PaxInstruments/labwiz-board/electronics/versions/labwiz-board-0.2/labwiz-board.brd

## EAGLE design electronics/versions/labwiz-board-0.2/labwiz-board.brd (2016-09-06)

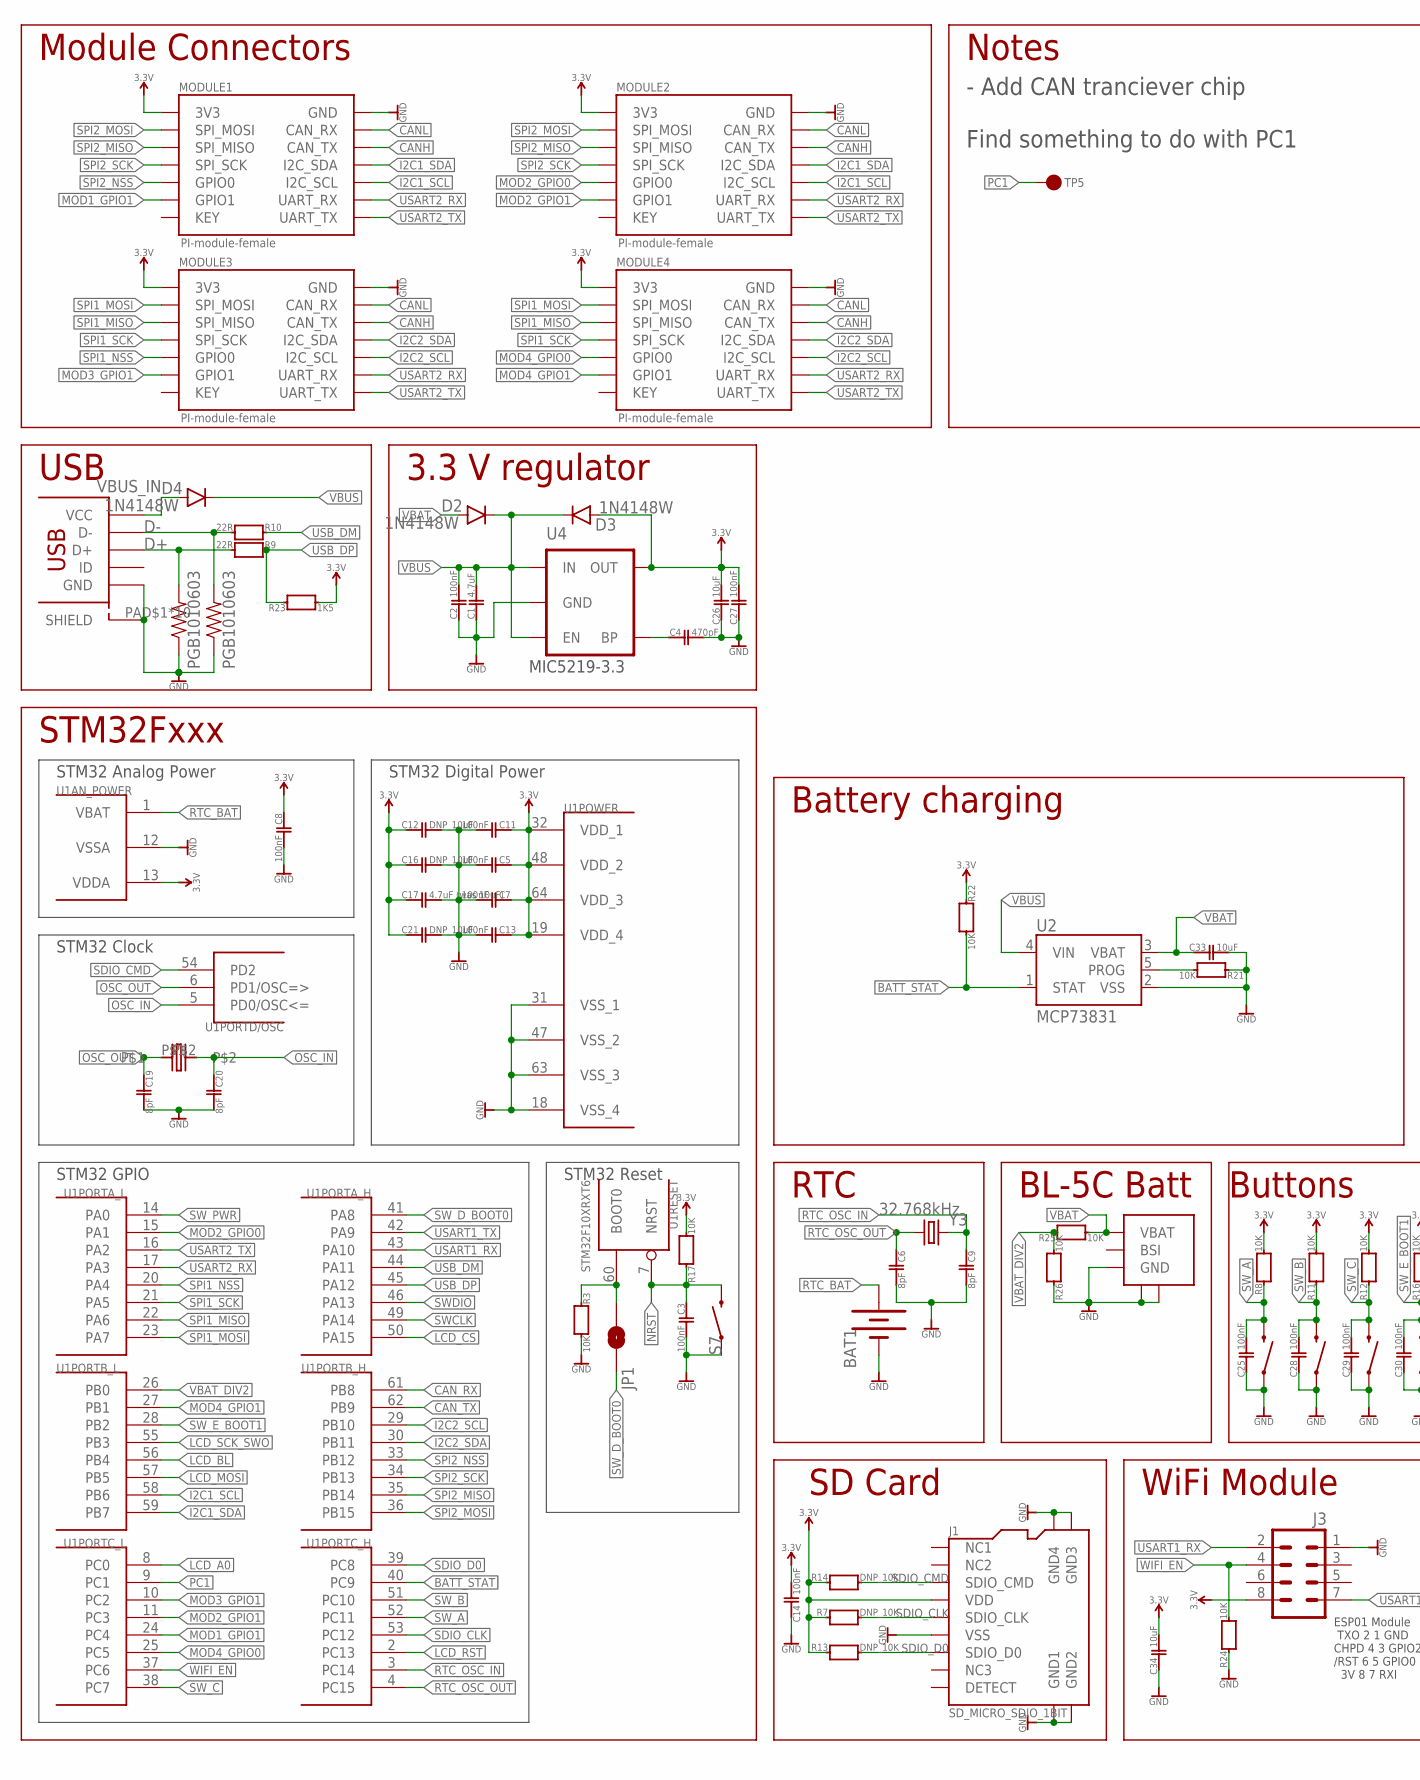
[picture p21: schematic labwiz-board.sch, sheet 1, part in row 1, column 1]

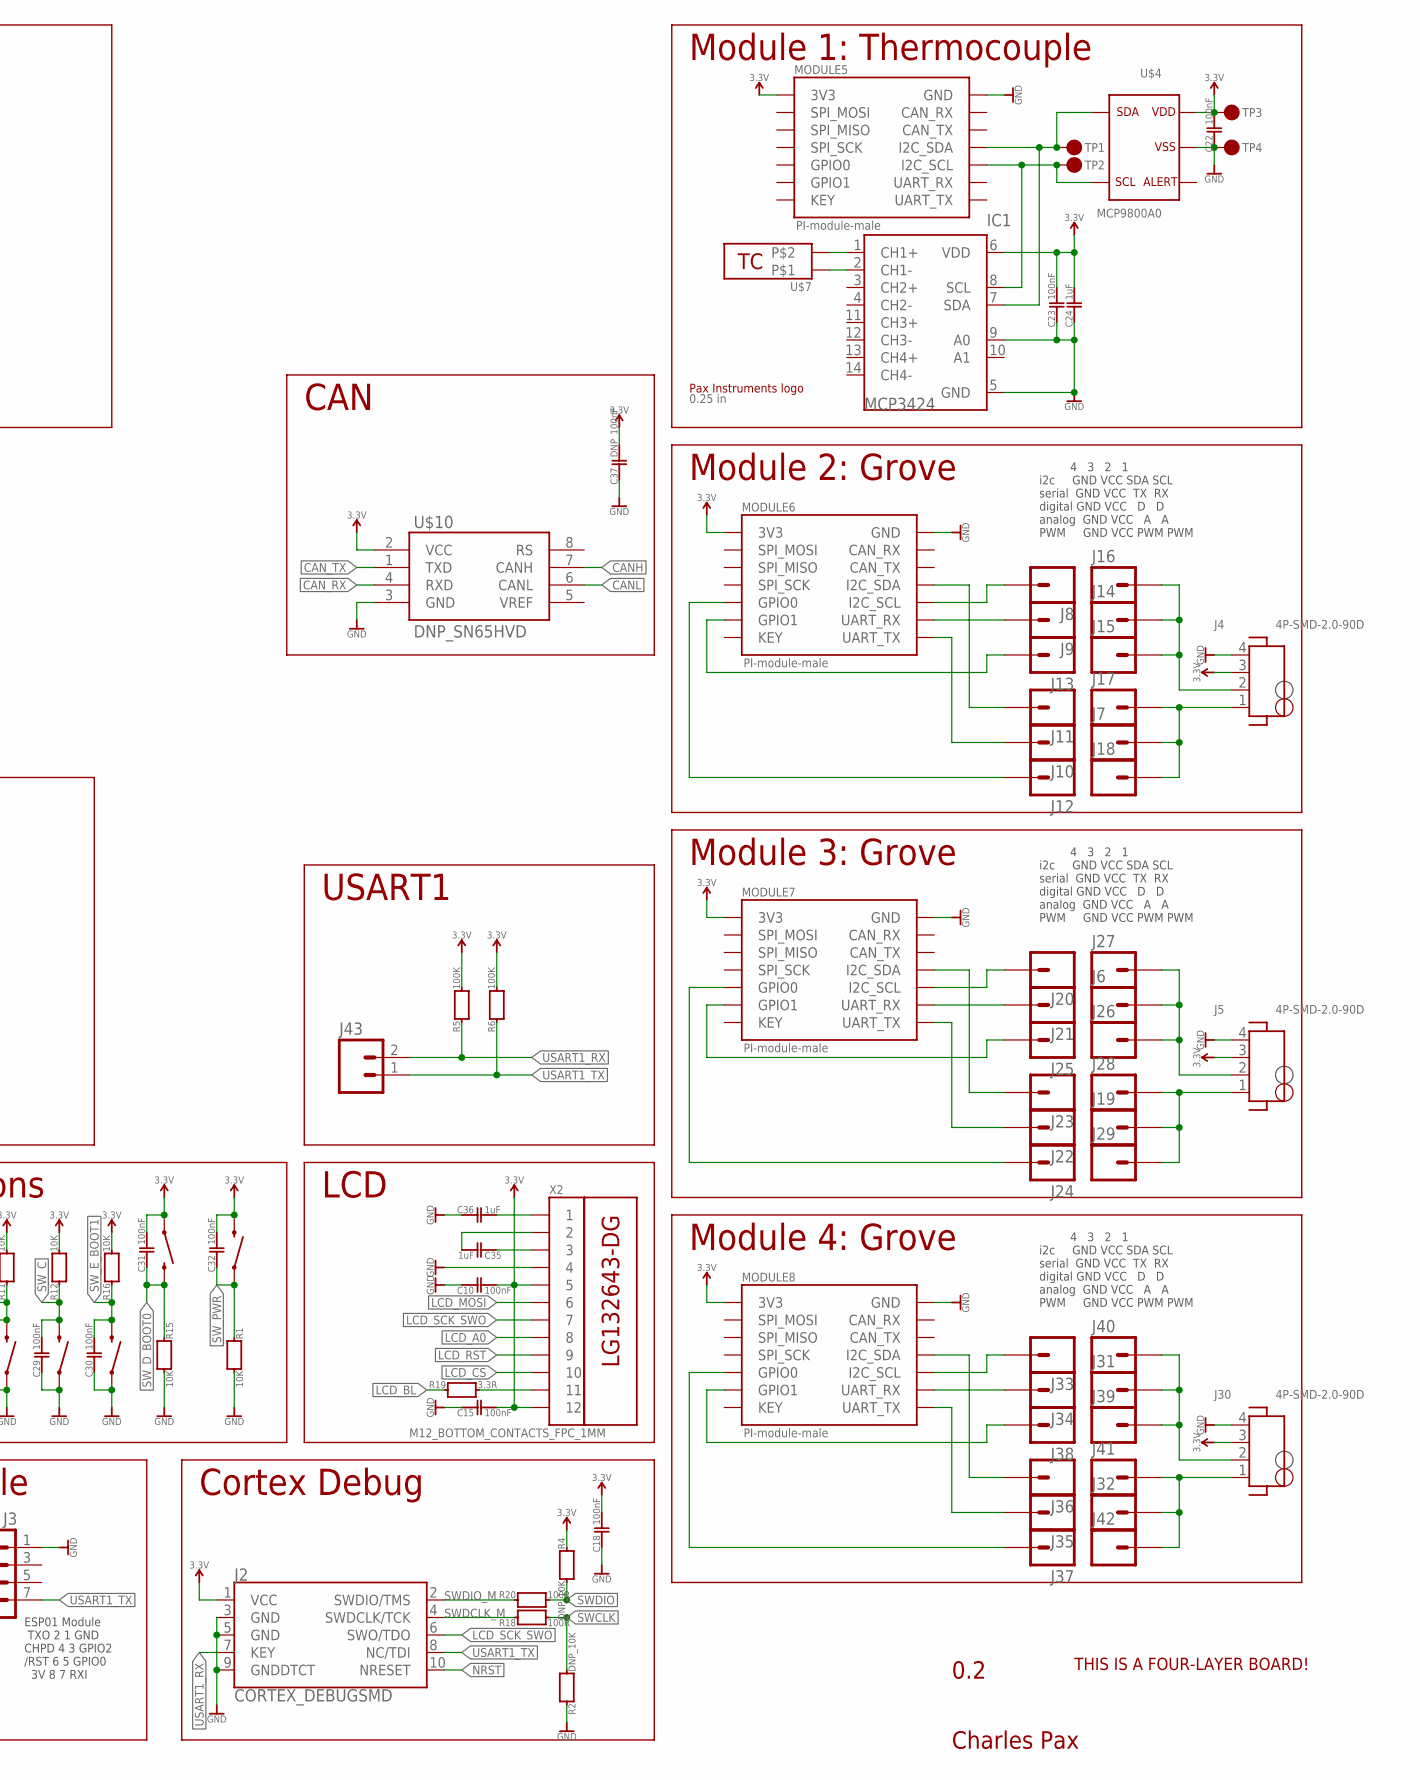
[picture p22: schematic labwiz-board.sch, sheet 1, part in row 1, column 2]

Parts:
BAT1: BATTERY12MM; BATTCON_12MM
C1: 4.7uF; 0402
C2, C3, C5, C7, C8, C10, C11, C13, C14, C15, C18, C22, C23, C25, C27, C28, C29, C30, C31, C32: 100nF; 0402
C4: 470pF; 0402
C6, C9, C19, C20: 8pF; 0402
C12, C16, C21: DNP_10uF; 0402
C17: 4.7uF (was 10uF); 0402
C24, C35, C36: 1uF; 0402
C26, C33, C34: 10uF; 0402
C37: DNP_100nF; 0402
D2, D3, D4: 1N4148W; SOD-123
IC1: MCP3424; SO14
J1: SD_MICRO_SDIO_1BIT; SD_MICRO_1
J2: CORTEX_DEBUGSMD; SAMTECH_FTSH-105-01
J3: M04X2; 2X4
J4, J5, J30: 4P-SMD-2.0-90D; HW4-SMD-2.0-90D
J6, J7, J8, J9, J10, J11, J12, J13, J14, J15, J16, J17, J18, J19, J20, J21, J22, J23, J24, J25, J26, J27, J28, J29, J31, J32, J33, J34, J35, J36, J37, J38, J39, J40, J41, J42: M01SMD-4.5X1.5; PAD-1.5X4.5
J43: M02PTH; 1X02
JP1: JUMPER-PAD-2-NOYES_SILK; PAD-JUMPER-2-NO_YES_SILK
MODULE1, MODULE2, MODULE3, MODULE4: PI-module-female; M07X2_2MM_EDGE
MODULE5, MODULE6, MODULE7, MODULE8: PI-module-male; M07X2_2MM_EDGE
R1, R3, R8, R11, R12, R15, R16, R17, R21, R22, R24, R25, R26: 10K; 0402
R2, R4, R7, R13, R14: DNP_10K; 0402
R5, R6: 100K; 0402
R9, R10: 22R; R0402
R18, R20: 100R; 0402
R19: 3.3R; 0402
R23: 1K5; R0402
S1, S2, S3, S4, S5, S6: SWITCH-MOMENTARY-2SMD; TACTILE_SWITCH_SMD; MPN RS-187R05A2-DS MT RT
S7: SWITCH-MOMENTARY-2SMD-3; TACTILE_SWITCH_SMD-3
TP1, TP2, TP3, TP4: M01_TH
TP5: M01_PAD_1MM; PAD_1MM
U1: STM32F10XRXT6; TQFP64
U2: MCP73831; SOT23-5
U4: MIC5219-3.3V; SOT23-5; MPN MIC5219-3.3YM5 TR
U$1: USB_MICROSMT+THRUHULE; USB_MICRO_THRUHOLE; MPN 10118194-0001LF
U$2: FOUR_LAYER_WARNING
U$3: BL-5C-CONNECTOR
U$4: MCP9800A0; SOT23-5L
U$5: LG132643-DG; MPN LG132643-DW
U$7: THERMOCOUPLE_MINI_INSIDE; THERMOCOUPLE_CLIP_INSIDE
U$9: NX3225GD
U$10: DNP_SN65HVD; SO08
U$13: 0.25 in; PAX-LOGO-0.25IN
X2: M12_BOTTOM_CONTACTS_FPC_1MM; FPC_12P_1MM
Y3: 32.768kHz; CRYSTAL-SMD-3.2X1.5MM
Z1, Z2: PGB1010603; SPARKFUN-RESISTORS_0603-RES; MPN PGB1010603NRHF

Connections:
3.3V: C5.1, C7.1, C8.1, C10.2, C11.1, C12.1, C13.1, C14.2, C15.2, C16.1, C17.1, C18.2, C21.1, C26.2, C27.2, C31.2, C32.2, C34.2, C37.2, D3.A, J1.4 (VDD), J2.1 (VCC), J3.8, MODULE1.P$1 (3V3), MODULE2.P$1 (3V3), MODULE3.P$1 (3V3), MODULE4.P$1 (3V3), R4.2, R5.1, R6.1, R7.2, R8.1, R11.1, R12.1, R13.2, R14.2, R16.1, R17.1, R22.2, R23.1, S4.1, S6.3 (2), U1.13 (VDDA), U1.19 (VDD_4), U1.32 (VDD_1), U1.48 (VDD_2), U1.64 (VDD_3), U4.5 (OUT), U$10.2 (VCC), X2.5, X2.12
3.3V_1: C22.2, C23.2, C24.2, IC1.6 (VDD), MODULE5.P$13 (3V3), TP3.P$1, U$4.1
3.3V_2: J4.3 (2), MODULE6.P$13 (3V3)
3.3V_3: J5.3 (2), MODULE7.P$13 (3V3)
3.3V_4: J30.3 (2), MODULE8.P$13 (3V3)
BATT_STAT: R22.1, U1.40 (PC9), U2.1 (STAT)
BOOT0: JP1.2, R3.2, U1.60 (BOOT0)
CANH: MODULE1.P$6 (CAN_TX), MODULE2.P$6 (CAN_TX), MODULE3.P$6 (CAN_TX), MODULE4.P$6 (CAN_TX), U$10.7 (CANH)
CANL: MODULE1.P$4 (CAN_RX), MODULE2.P$4 (CAN_RX), MODULE3.P$4 (CAN_RX), MODULE4.P$4 (CAN_RX), U$10.6 (CANL)
CAN_RX: U1.61 (PB8), U$10.4 (RXD)
CAN_TX: U1.62 (PB9), U$10.1 (TXD)
D+: R9.1, U$1.PIN$3 (D+), Z1.2
D-: R10.1, U$1.PIN$2 (D-), Z2.2
GND: BAT1.GND (-), C1.1, C2.1, C3.2, C4.2, C5.2, C6.2, C7.2, C8.2, C9.2, C10.1, C11.2, C12.2, C13.2, C14.1, C15.1, C16.2, C17.2, C18.1, C19.2, C20.2, C21.2, C25.1, C26.1, C27.1, C28.1, C29.1, C30.1, C33.2, C34.1, C36.1, C37.1, J1.6 (VSS), J1.G1 (GND1), J1.G2 (GND2), J1.G3 (GND3), J1.G4 (GND4), J2.3 (GND), J2.5 (GND), J2.9 (GNDDTCT), J3.1, MODULE1.P$2 (GND), MODULE2.P$2 (GND), MODULE3.P$2 (GND), MODULE4.P$2 (GND), R1.1, R2.2, R3.1, R15.1, R21.2, R24.2, R26.2, S1.1, S2.1, S3.1, S5.1, S7.1, U1.12 (VSSA), U1.18 (VSS_4), U1.31 (VSS_1), U1.47 (VSS_2), U1.63 (VSS_3), U2.2 (VSS), U4.2 (GND), U$1.PAD$1 (SHIELD), U$1.PAD$2 (SHIELD), U$1.PAD$3 (SHIELD), U$1.PAD$4 (SHIELD), U$1.PAD$5 (SHIELD), U$1.PAD$6 (SHIELD), U$1.PAD$7 (SHIELD), U$1.PAD$8 (SHIELD), U$1.PAD$9 (SHIELD), U$1.PAD$10 (SHIELD), U$1.PIN$5 (GND), U$3.P$3 (GND), U$3.P$4, U$3.P$5, U$10.3 (GND), X2.4, Z1.1, Z2.1
GND_1: C22.1, C23.1, C24.1, IC1.5 (GND), IC1.9 (A0), MODULE5.P$14 (GND), TP4.P$1, U$4.2
GND_2: J4.4 (1), MODULE6.P$14 (GND)
GND_3: J5.4 (1), MODULE7.P$14 (GND)
GND_4: J30.4 (1), MODULE8.P$14 (GND)
I2C1_SCL: MODULE1.P$10 (I2C_SCL), MODULE2.P$10 (I2C_SCL), U1.58 (PB6)
I2C1_SDA: MODULE1.P$8 (I2C_SDA), MODULE2.P$8 (I2C_SDA), U1.59 (PB7)
I2C2_SCL: MODULE3.P$10 (I2C_SCL), MODULE4.P$10 (I2C_SCL), U1.29 (PB10)
I2C2_SDA: MODULE3.P$8 (I2C_SDA), MODULE4.P$8 (I2C_SDA), U1.30 (PB11)
LCD_A0: U1.8 (PC0), X2.8
LCD_BL: R19.2, U1.56 (PB4)
LCD_CS: U1.50 (PA15), X2.10
LCD_MOSI: U1.57 (PB5), X2.6
LCD_RST: U1.2 (PC13), X2.9
LCD_SCK_SWO: J2.6 (SWO/TDO), U1.55 (PB3), X2.7
MOD1_GPIO1: MODULE1.P$11 (GPIO1), U1.24 (PC4)
MOD2_GPIO0: MODULE2.P$9 (GPIO0), U1.15 (PA1)
MOD2_GPIO1: MODULE2.P$11 (GPIO1), U1.11 (PC3)
MOD3_GPIO1: MODULE3.P$11 (GPIO1), U1.10 (PC2)
MOD4_GPIO0: MODULE4.P$9 (GPIO0), U1.25 (PC5)
MOD4_GPIO1: MODULE4.P$11 (GPIO1), U1.27 (PB1)
unnamed: C4.1, U4.4 (BP)
unnamed: R19.1, X2.11
unnamed: J4.2 (3), J14.P$1, J15.P$1, J16.P$1
unnamed: J5.2 (3), J6.P$1, J26.P$1, J27.P$1
unnamed: IC1.2 (CH1-), U$7.P$1
unnamed: IC1.1 (CH1+), U$7.P$2
unnamed: C35.1, X2.3
unnamed: C35.2, X2.2
unnamed: C36.2, X2.1
unnamed: J4.1 (4), J7.P$1, J17.P$1, J18.P$1
unnamed: J5.1 (4), J19.P$1, J28.P$1, J29.P$1
unnamed: J20.P$1, MODULE7.P$6 (I2C_SCL)
unnamed: J21.P$1, MODULE7.P$4 (UART_RX)
unnamed: J8.P$1, MODULE6.P$6 (I2C_SCL)
unnamed: J9.P$1, MODULE6.P$4 (UART_RX)
unnamed: J10.P$1, MODULE6.P$2 (UART_TX)
unnamed: J11.P$1, MODULE6.P$8 (I2C_SDA)
unnamed: J13.P$1, MODULE6.P$3 (GPIO1)
unnamed: J12.P$1, MODULE6.P$5 (GPIO0)
unnamed: J22.P$1, MODULE7.P$2 (UART_TX)
unnamed: J23.P$1, MODULE7.P$8 (I2C_SDA)
unnamed: J25.P$1, MODULE7.P$3 (GPIO1)
unnamed: J24.P$1, MODULE7.P$5 (GPIO0)
unnamed: J30.2 (3), J31.P$1, J39.P$1, J40.P$1
unnamed: J30.1 (4), J32.P$1, J41.P$1, J42.P$1
unnamed: J33.P$1, MODULE8.P$6 (I2C_SCL)
unnamed: J34.P$1, MODULE8.P$4 (UART_RX)
unnamed: J35.P$1, MODULE8.P$2 (UART_TX)
unnamed: J36.P$1, MODULE8.P$8 (I2C_SDA)
unnamed: J38.P$1, MODULE8.P$3 (GPIO1)
unnamed: J37.P$1, MODULE8.P$5 (GPIO0)
unnamed: R21.1, U2.5 (PROG)
NRST: C3.1, J2.10 (NRESET), R17.2, S7.4 (2), U1.7 (NRST)
OSC_IN: C20.1, U1.5 (PD0/OSC<=), U$9.P$2
OSC_OUT: C19.1, U1.6 (PD1/OSC=>), U$9.P$1
PC1: TP5.P$1, U1.9 (PC1)
RTC_BAT: BAT1.PWR@1 (+), U1.1 (VBAT)
RTC_OSC_IN: C9.1, U1.3 (PC14), Y3.P$2 (2)
RTC_OSC_OUT: C6.1, U1.4 (PC15), Y3.P$1 (1)
SCL_1: IC1.8 (SCL), MODULE5.P$6 (I2C_SCL), TP2.P$1, U$4.4
SDA_1: IC1.7 (SDA), MODULE5.P$8 (I2C_SDA), TP1.P$1, U$4.5
SDIO_CLK: J1.5 (SDIO_CLK), R7.1, U1.53 (PC12)
SDIO_CMD: J1.3 (SDIO_CMD), R14.1, U1.54 (PD2)
SDIO_D0: J1.7 (SDIO_D0), R13.1, U1.39 (PC8)
SPI1_MISO: MODULE3.P$5 (SPI_MISO), MODULE4.P$5 (SPI_MISO), U1.22 (PA6)
SPI1_MOSI: MODULE3.P$3 (SPI_MOSI), MODULE4.P$3 (SPI_MOSI), U1.23 (PA7)
SPI1_NSS: MODULE3.P$9 (GPIO0), U1.20 (PA4)
SPI1_SCK: MODULE3.P$7 (SPI_SCK), MODULE4.P$7 (SPI_SCK), U1.21 (PA5)
SPI2_MISO: MODULE1.P$5 (SPI_MISO), MODULE2.P$5 (SPI_MISO), U1.35 (PB14)
SPI2_MOSI: MODULE1.P$3 (SPI_MOSI), MODULE2.P$3 (SPI_MOSI), U1.36 (PB15)
SPI2_NSS: MODULE1.P$9 (GPIO0), U1.33 (PB12)
SPI2_SCK: MODULE1.P$7 (SPI_SCK), MODULE2.P$7 (SPI_SCK), U1.34 (PB13)
SWCLK: R2.1, R18.1, U1.49 (PA14)
SWDCLK_M: J2.4 (SWDCLK/TCK), R18.2
SWDIO: R4.1, R20.1, U1.46 (PA13)
SWDIO_M: J2.2 (SWDIO/TMS), R20.2
SW_A: C25.2, R8.2, S3.3 (2), U1.52 (PC11)
SW_B: C28.2, R11.2, S2.3 (2), U1.51 (PC10)
SW_C: C29.2, R12.2, S1.3 (2), U1.38 (PC7)
SW_D_BOOT0: C31.1, JP1.1, R15.2, S4.3 (2), U1.41 (PA8)
SW_E_BOOT1: C30.2, R16.2, S5.3 (2), U1.28 (PB2)
SW_PWR: C32.1, R1.2, S6.1, U1.14 (PA0)
USART1_RX: J2.7 (KEY), J3.2, J43.2, R5.2, U1.43 (PA10)
USART1_TX: J2.8 (NC/TDI), J3.7, J43.1, R6.2, U1.42 (PA9)
USART2_RX: MODULE1.P$12 (UART_RX), MODULE2.P$12 (UART_RX), MODULE3.P$12 (UART_RX), MODULE4.P$12 (UART_RX), U1.17 (PA3)
USART2_TX: MODULE1.P$14 (UART_TX), MODULE2.P$14 (UART_TX), MODULE3.P$14 (UART_TX), MODULE4.P$14 (UART_TX), U1.16 (PA2)
USB_DM: R10.2, U1.44 (PA11)
USB_DP: R9.2, R23.2, U1.45 (PA12)
VBAT: C33.1, D2.A, R25.1, U2.3 (VBAT), U$3.P$1 (VBAT)
VBAT_DIV2: R25.2, R26.1, U1.26 (PB0)
VBUS: C1.2, C2.2, D2.C, D3.C, D4.C, U2.4 (VIN), U4.1 (IN), U4.3 (EN)
VBUS_IN: D4.A, U$1.PIN$1 (VCC)
WIFI_EN: J3.4, R24.1, U1.37 (PC6)

Notes on the sheet:
MIC5219-3.3
USB
3.3 V regulator
LCD
Buttons
0.2
Charles Pax
SD Card
STM32 Digital Power
STM32 Analog Power
STM32 Clock
STM32 Reset
STM32Fxxx
STM32 GPIO
RTC
Module Connectors
BL-5C Batt
Cortex Debug
Module 1: Thermocouple
Module 2: Grove
- Add CAN tranciever chip
ESP01 Module TXO 2 1 GND CHPD 4 3 GPIO2 /RST 6 5 GPIO0 3V 8 7 RXI
WiFi Module
4 3 2 1 i2c GND VCC SDA SCL serial GND VCC TX RX digital GND VCC D D analog GND VCC A A PWM GND VCC PWM PWM
Module 3: Grove
Module 4: Grove
Battery charging
USART1
Notes
Find something to do with PC1
CAN

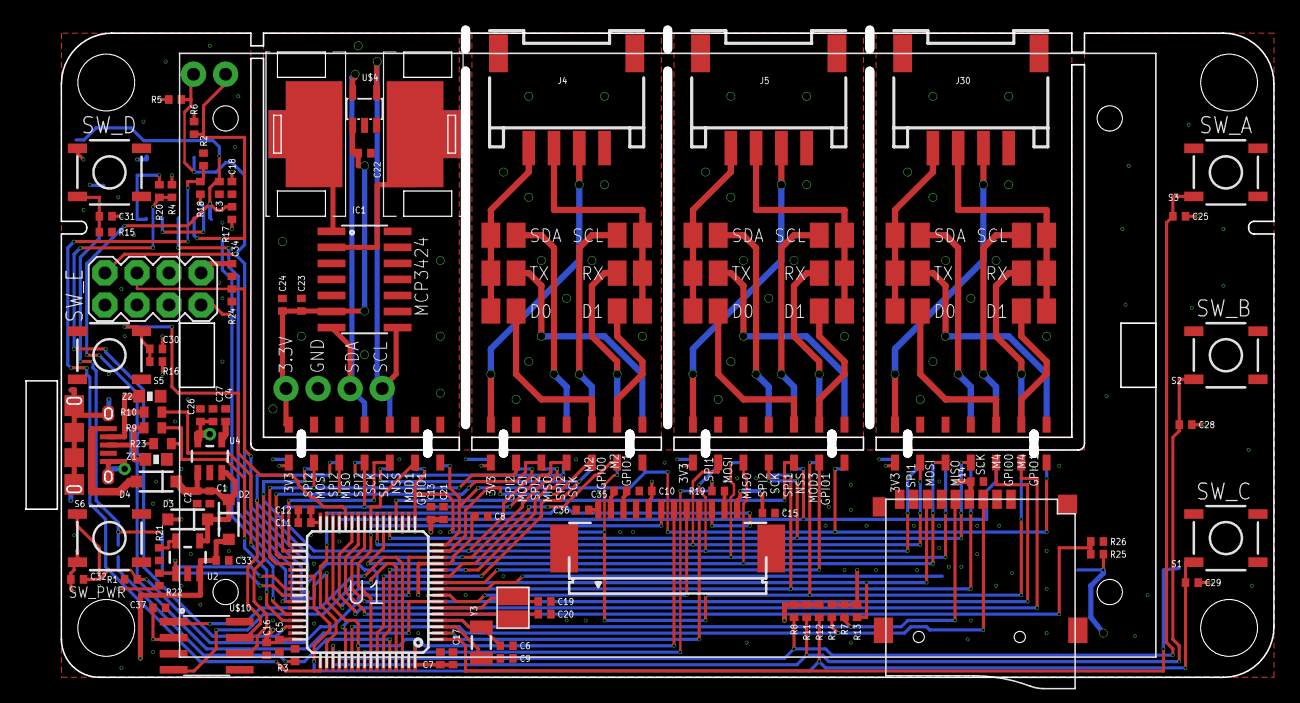
[picture p23: board electronics/versions/labwiz-board-0.2/labwiz-board.brd from above]

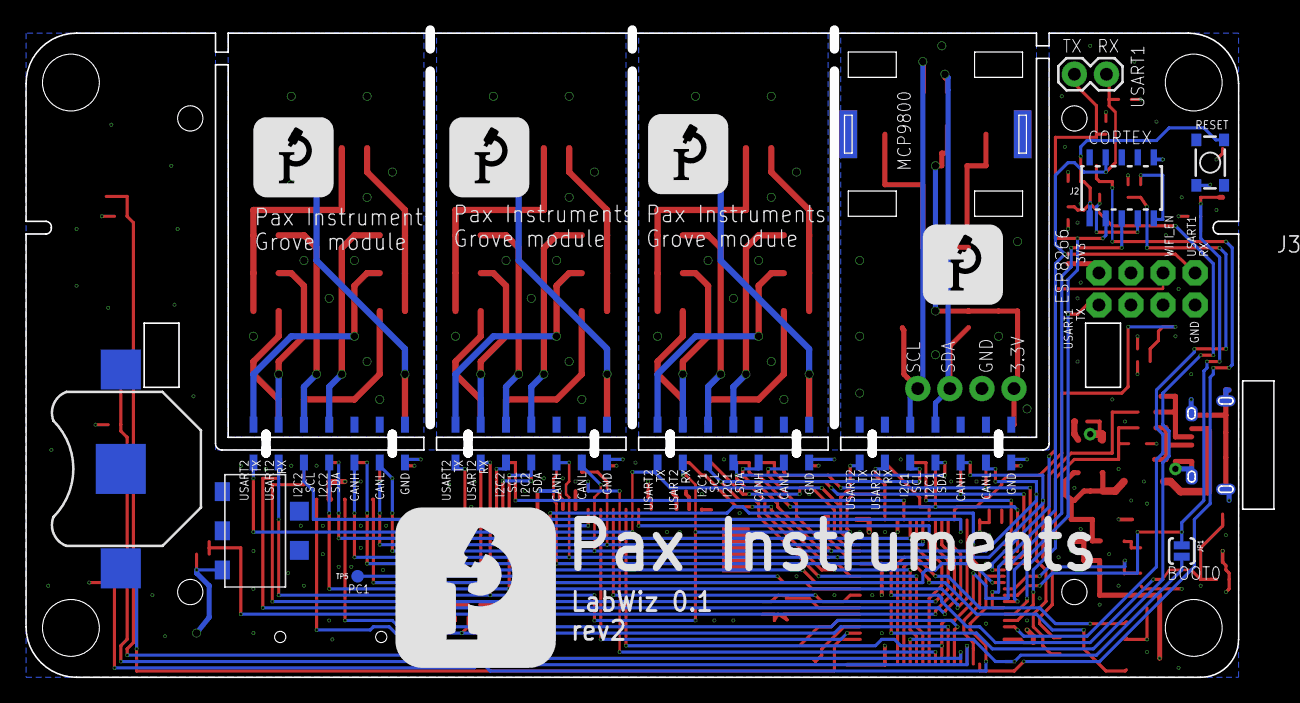
[picture p24: board electronics/versions/labwiz-board-0.2/labwiz-board.brd from below]

Board: 4 copper layers, 98.8 x 51.2 mm, 152 parts (13 on the bottom side), 107 nets.

Other parts of the board:
U$6: PAX-LOGO-0.5IN
U$8, U$11, U$12: 0.25 in; PAX-LOGO-0.25IN
