PaxInstruments/labwiz-board/electronics/versions/labwiz-board-v0.1.1/armwiz-board.brd

## EAGLE design electronics/versions/labwiz-board-v0.1.1/armwiz-board.brd (2016-08-08)

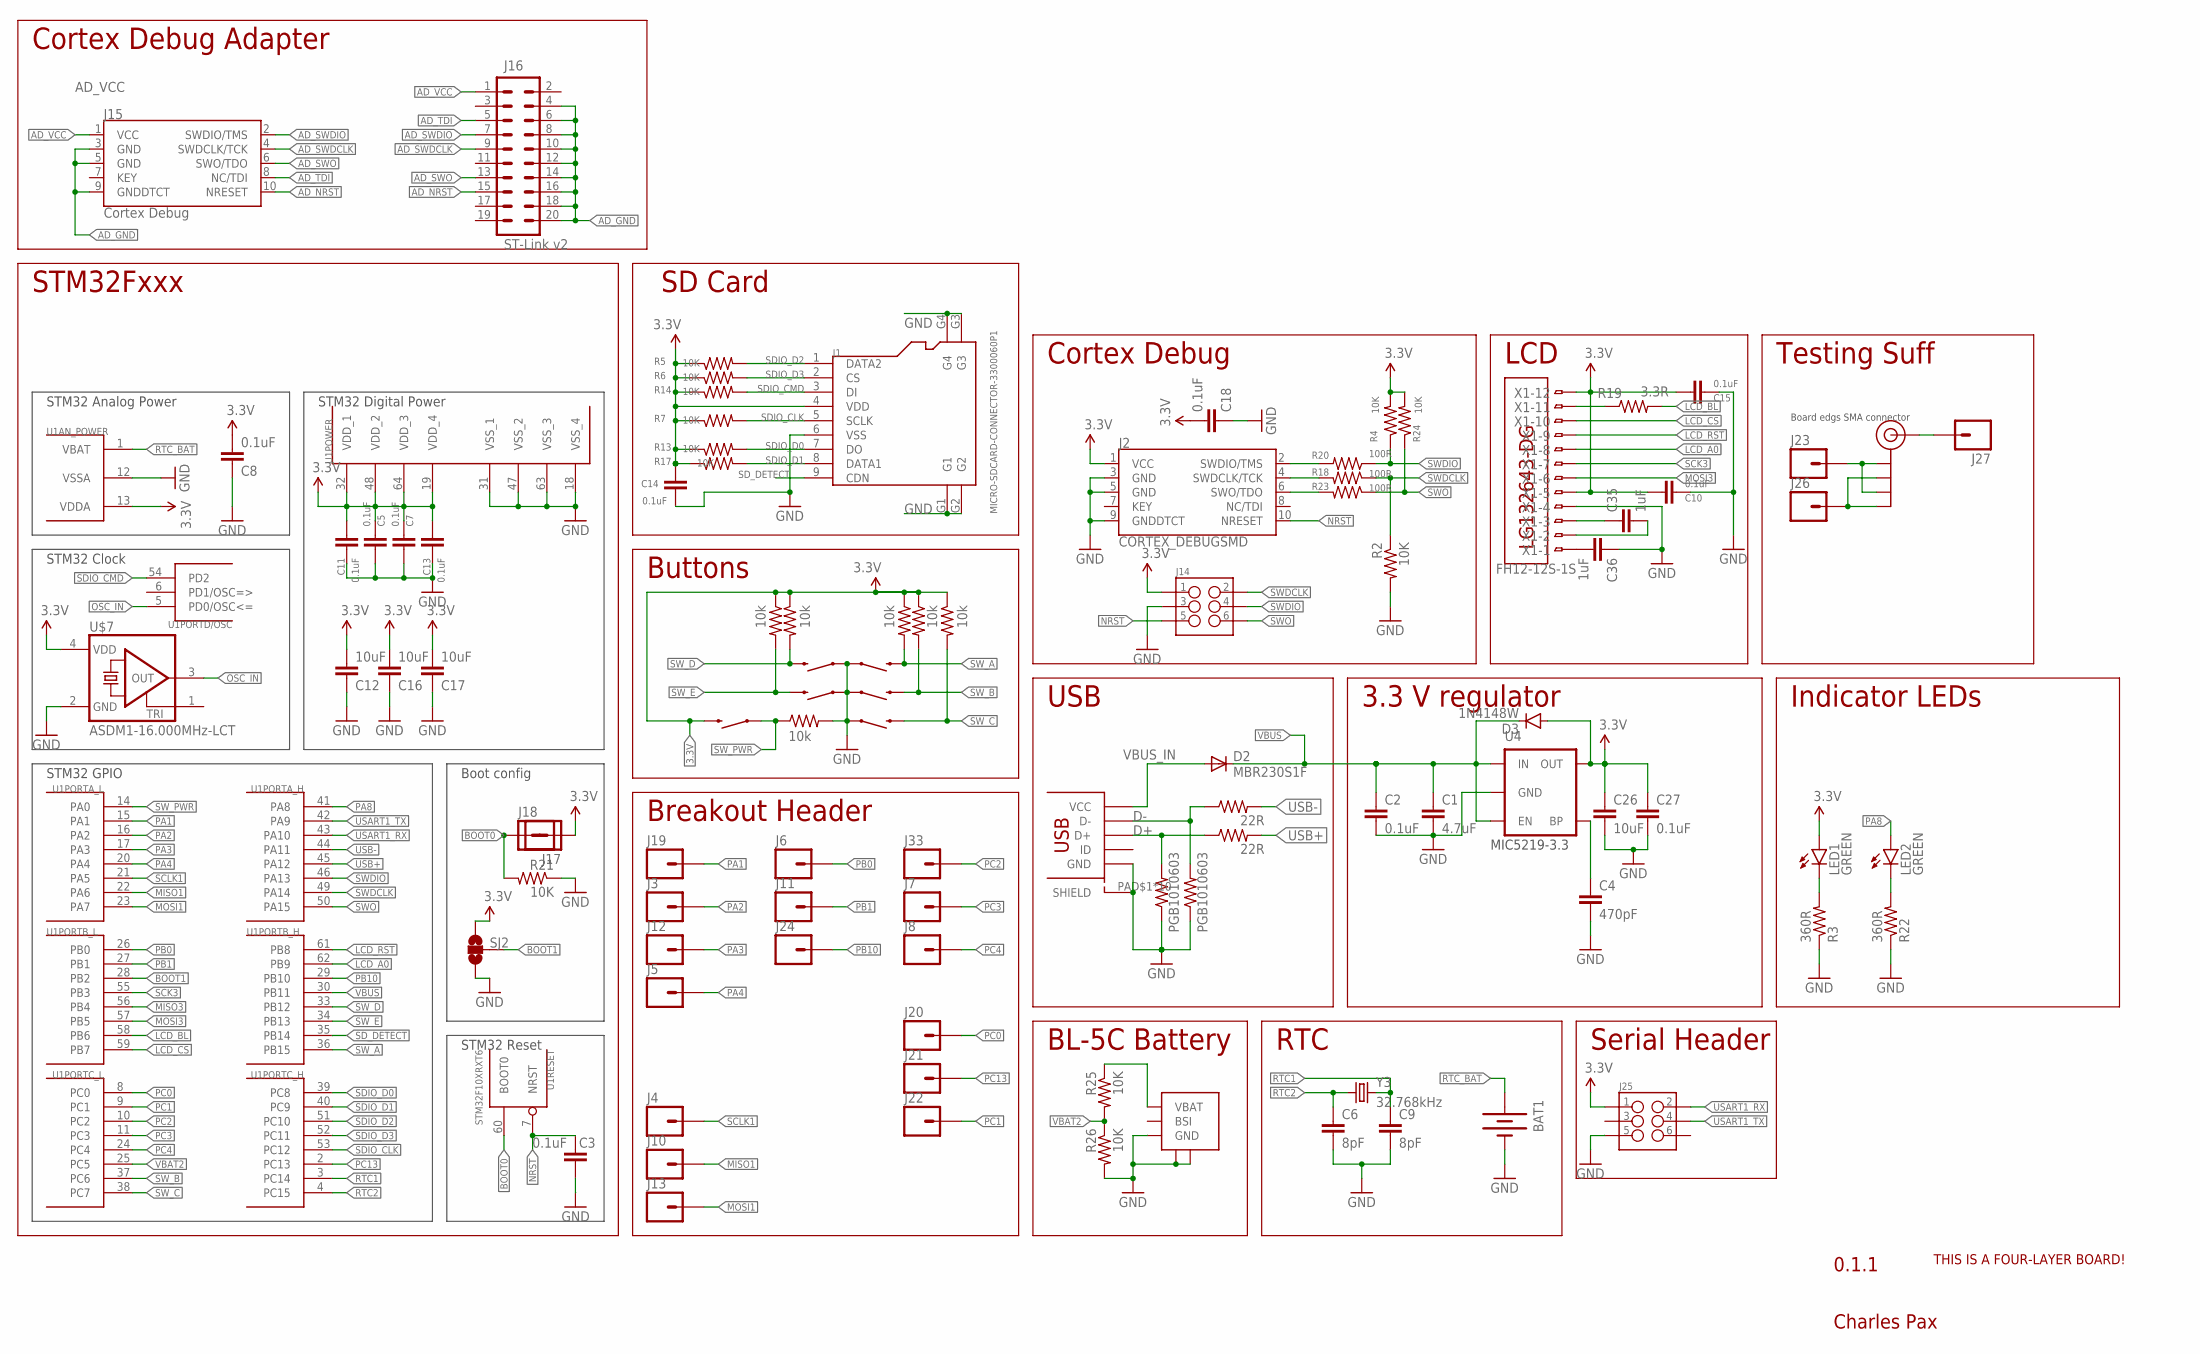
[picture p25: schematic armwiz-board.sch]

Parts:
BAT1: BATTERY12MM; BATTCON_12MM
C1: 4.7uF; C0402K
C2, C3, C5, C7, C8, C10, C11, C13, C14, C15, C18, C27: 0.1uF; C0402K
C4: 470pF; C0402K
C6, C9: 8pF; C0402K
C12, C16, C17, C26: 10uF; C0402K
C35, C36: 1uF; C0402K
D2: MBR230S1F; SOD123; MPN MBR230S1F-7
D3: 1N4148W; SOD-123
J1: MICRO-SDCARD-CONNECTOR-3300060P1; 9P-SMD-W-RING; MPN ST-TF-003A
J2: CORTEX_DEBUGSMD; SAMTECH_FTSH-105-01
J3, J4, J5, J6, J7, J8, J10, J11, J12, J13, J19, J20, J21, J22, J23, J24, J26, J27, J33: M01PTH; 1X01
J14, J25: M03X2PAX; CONNECTORS_2X3_SMT_POSTS_T400
J15: Cortex Debug; SAMTECH_FTSH-105-01
J16: ST-Link v2; 2X10
J17, J18: M01NOSILK-KIT; 1X01NS-KIT
J$1: SMA_EDGE; SMA-EDGE
LED1, LED2: GREEN; LED-0603
R1, R8, R11, R12, R15, R16: 10k; R0402
R2, R4, R5, R6, R7, R13, R14, R17, R21, R24, R25, R26: 10K; R0402
R3, R22: 360R; R0402
R9, R10: 22R; R0402
R18, R20, R23: 100R; R0402
R19: 3.3R; R0402
S1, S2, S3, S4, S5, S6: SWITCH-MOMENTARY-2SMD; TACTILE_SWITCH_SMD; MPN RS-187R05A2-DS MT RT
SJ2: SOLDERJUMPER_2WAYS; SJ_3
U1: STM32F10XRXT6; TQFP64
U4: MIC5219-3.3V; SOT23-5; MPN MIC5219-3.3YM5 TR
U$1: USB_MICROSMT+THRUHULE; USB_MICRO_THRUHOLE; MPN 10118194-0001LF
U$2: FOUR_LAYER_WARNING
U$3: BL-5C-CONNECTOR
U$5: LG132643-DG; MPN LG132643-DW
U$7: ASDM1-16.000MHz-LCT; ASE
X1: FH12-12S-1S; FH12-12S-1SH; MPN FH12-12S-1SH(55)
Y3: 32.768kHz; CRYSTAL-SMD-3.2X1.5MM
Z1, Z2: PGB1010603; SPARKFUN-RESISTORS_0603-RES; MPN PGB1010603NRHF

Connections:
3.3V: C5.1, C7.1, C8.2, C10.2, C11.2, C12.2, C13.2, C14.2, C15.2, C16.2, C17.2, C18.2, C26.1, C27.1, D3.A, J1.4 (VDD), J2.1 (VCC), J14.1, J18.1, J25.1, LED1.A, R4.2, R5.1, R6.1, R7.1, R8.1, R11.1, R12.1, R13.1, R14.1, R15.1, R16.1, R17.1, R24.2, S6.3 (2), SJ2.3, U1.13 (VDDA), U1.19 (VDD_4), U1.32 (VDD_1), U1.48 (VDD_2), U1.64 (VDD_3), U4.5 (OUT), U$7.4 (VDD), X1.5, X1.12
AD_GND: J15.3 (GND), J15.5 (GND), J15.9 (GNDDTCT), J16.4, J16.6, J16.8, J16.10, J16.12, J16.14, J16.16, J16.18, J16.20
AD_NRST: J15.10 (NRESET), J16.15
AD_SWDCLK: J15.4 (SWDCLK/TCK), J16.9
AD_SWDIO: J15.2 (SWDIO/TMS), J16.7
AD_SWO: J15.6 (SWO/TDO), J16.13
AD_TDI: J15.8 (NC/TDI), J16.5
AD_VCC: J15.1 (VCC), J16.1
BOOT0: J17.1, R21.2, U1.60 (BOOT0)
BOOT1: SJ2.2, U1.28 (PB2)
D+: R9.1, U$1.PIN$3 (D+), Z1.2
D-: R10.1, U$1.PIN$2 (D-), Z2.2
GND: BAT1.GND (-), C1.2, C2.2, C3.2, C4.2, C5.2, C6.2, C7.2, C8.1, C9.2, C10.1, C11.1, C12.1, C13.1, C14.1, C15.1, C16.1, C17.1, C18.1, C26.2, C27.2, C36.1, J1.6 (VSS), J1.G1, J1.G2, J1.G3, J1.G4, J2.3 (GND), J2.5 (GND), J2.9 (GNDDTCT), J14.3, J25.5, R1.2, R2.2, R3.1, R21.1, R22.1, R26.2, S1.1, S2.1, S3.1, S4.1, S5.1, SJ2.1, U1.12 (VSSA), U1.18 (VSS_4), U1.31 (VSS_1), U1.47 (VSS_2), U1.63 (VSS_3), U4.2 (GND), U$1.PAD$1 (SHIELD), U$1.PAD$2 (SHIELD), U$1.PAD$3 (SHIELD), U$1.PAD$4 (SHIELD), U$1.PAD$5 (SHIELD), U$1.PAD$6 (SHIELD), U$1.PAD$7 (SHIELD), U$1.PAD$8 (SHIELD), U$1.PAD$9 (SHIELD), U$1.PAD$10 (SHIELD), U$1.PIN$5 (GND), U$3.P$3 (GND), U$3.P$4, U$3.P$5, U$7.2 (GND), X1.4, Z1.1, Z2.1
LCD_A0: U1.62 (PB9), X1.8
LCD_BL: R19.2, U1.58 (PB6)
LCD_CS: U1.59 (PB7), X1.10
LCD_RST: U1.61 (PB8), X1.9
MISO1: J10.1, U1.22 (PA6)
MISO3: U1.56 (PB4)
MOSI1: J13.1, U1.23 (PA7)
MOSI3: U1.57 (PB5), X1.6
unnamed: C4.1, U4.4 (BP)
unnamed: R19.1, X1.11
unnamed: J2.4 (SWDCLK/TCK), R18.2
unnamed: LED1.C, R3.2
unnamed: LED2.C, R22.2
unnamed: J2.6 (SWO/TDO), R23.2
unnamed: J2.2 (SWDIO/TMS), R20.2
unnamed: J26.1, J$1.GND@1 (GND), J$1.GND@3 (GND)
unnamed: J23.1, J$1.GND@0 (GND), J$1.GND@2 (GND)
unnamed: R25.1, U$3.P$1 (VBAT)
unnamed: J27.1, J$1.SIG (SIGNAL)
unnamed: C35.1, X1.3
unnamed: C35.2, X1.2
unnamed: C36.2, X1.1
NRST: C3.1, J2.10 (NRESET), J14.5, U1.7 (NRST)
OSC_IN: U1.5 (PD0/OSC<=), U$7.3 (OUT)
PA1: J19.1, U1.15 (PA1)
PA2: J3.1, U1.16 (PA2)
PA3: J12.1, U1.17 (PA3)
PA4: J5.1, U1.20 (PA4)
PA8: LED2.A, U1.41 (PA8)
PB0: J6.1, U1.26 (PB0)
PB1: J11.1, U1.27 (PB1)
PB10: J24.1, U1.29 (PB10)
PC0: J20.1, U1.8 (PC0)
PC1: J22.1, U1.9 (PC1)
PC2: J33.1, U1.10 (PC2)
PC3: J7.1, U1.11 (PC3)
PC4: J8.1, U1.24 (PC4)
PC13: J21.1, U1.2 (PC13)
RTC1: C9.1, U1.3 (PC14), Y3.P$2 (2)
RTC2: C6.1, U1.4 (PC15), Y3.P$1 (1)
RTC_BAT: BAT1.PWR@1 (+), U1.1 (VBAT)
SCK3: U1.55 (PB3), X1.7
SCLK1: J4.1, U1.21 (PA5)
SDIO_CLK: J1.5 (SCLK), R7.2, U1.53 (PC12)
SDIO_CMD: J1.3 (DI), R14.2, U1.54 (PD2)
SDIO_D0: J1.7 (DO), R13.2, U1.39 (PC8)
SDIO_D1: J1.8 (DATA1), R17.2, U1.40 (PC9)
SDIO_D2: J1.1 (DATA2), R5.2, U1.51 (PC10)
SDIO_D3: J1.2 (CS), R6.2, U1.52 (PC11)
SD_DETECT: J1.9 (CDN), U1.35 (PB14)
SWDCLK: J14.2, R2.1, R18.1, U1.49 (PA14)
SWDIO: J14.4, R4.1, R20.1, U1.46 (PA13)
SWO: J14.6, R23.1, R24.1, U1.50 (PA15)
SW_A: R8.2, S3.3 (2), U1.36 (PB15)
SW_B: R11.2, S2.3 (2), U1.37 (PC6)
SW_C: R12.2, S1.3 (2), U1.38 (PC7)
SW_D: R15.2, S4.3 (2), U1.33 (PB12)
SW_E: R16.2, S5.3 (2), U1.34 (PB13)
SW_PWR: R1.1, S6.1, U1.14 (PA0)
USART1_RX: J25.2, U1.43 (PA10)
USART1_TX: J25.4, U1.42 (PA9)
USB+: R9.2, U1.45 (PA12)
USB-: R10.2, U1.44 (PA11)
VBAT2: R25.2, R26.1, U1.25 (PC5)
VBUS: C1.1, C2.1, D2.C, D3.C, U1.30 (PB11), U4.1 (IN), U4.3 (EN)
VBUS_IN: D2.A, U$1.PIN$1 (VCC)

Notes on the sheet:
MIC5219-3.3
USB
3.3 V regulator
LCD
Buttons
0.1.1
Charles Pax
SD Card
STM32 Digital Power
STM32 Analog Power
STM32 Clock
STM32 Reset
STM32Fxxx
STM32 GPIO
Serial Header
RTC
Breakout Header
BL-5C Battery
Boot config
Cortex Debug
Cortex Debug Adapter
Indicator LEDs
Testing Suff
Board edgs SMA connector

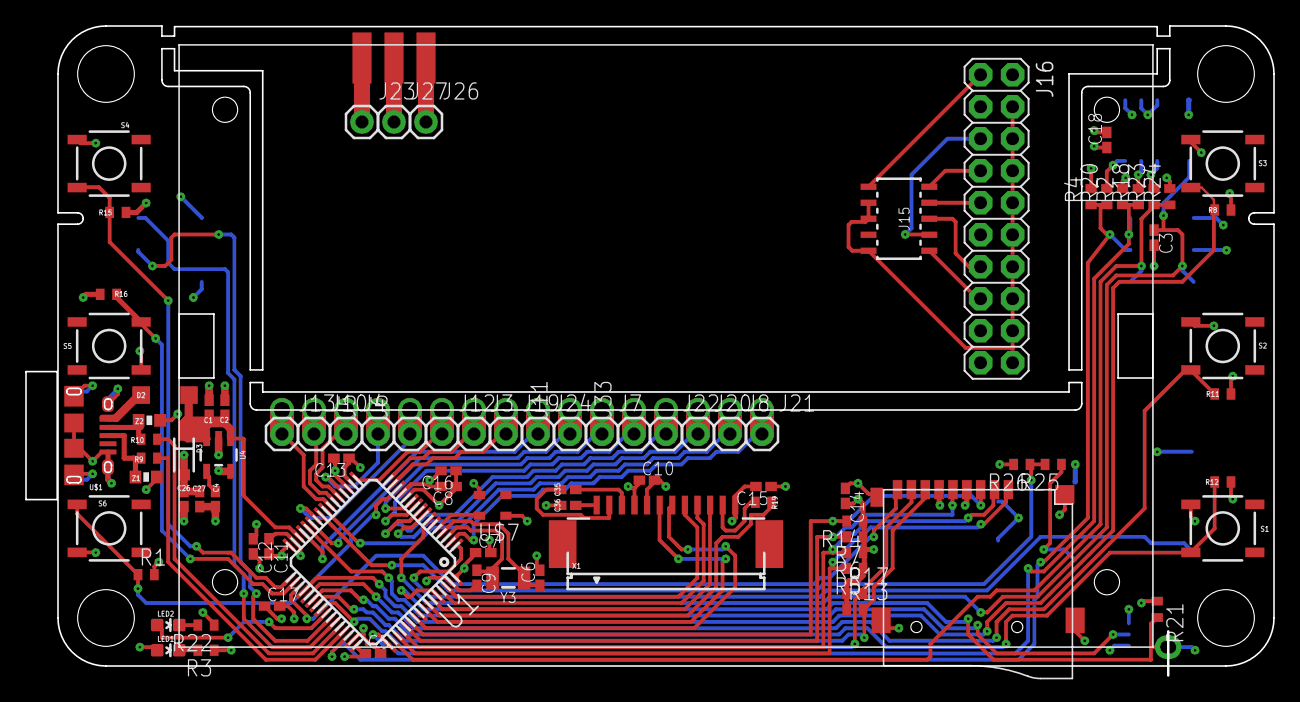
[picture p26: board armwiz-board.brd from above]

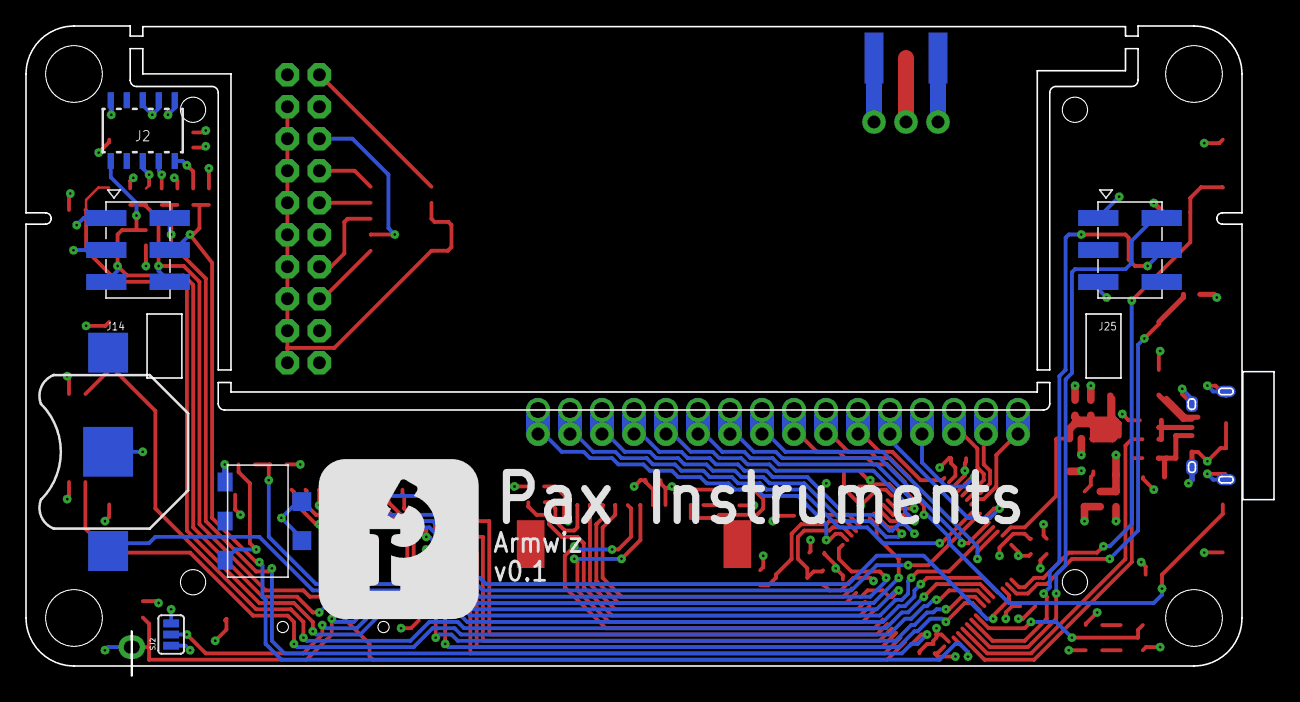
[picture p27: board armwiz-board.brd from below]

Board: 4 copper layers, 99.1 x 51.5 mm, 100 parts (8 on the bottom side), 78 nets.

Other parts of the board:
U$6: PAX-LOGO-0.5IN
